AdmiralLuckytiger/OsciBoard/Documentation/Images/Full Wave Precision Rectifier/A.jpeg

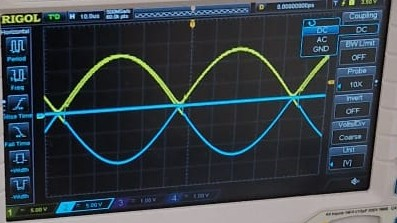
Documentation/Images/Full Wave Precision Rectifier/A.jpeg
