AdmiralLuckytiger/OsciBoard/Documentation/Images/Full Wave Precision Rectifier/B.jpeg

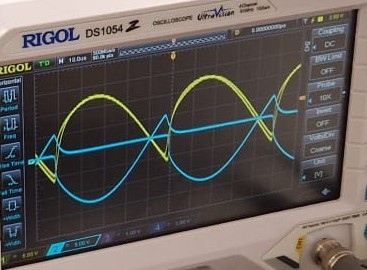
Documentation/Images/Full Wave Precision Rectifier/B.jpeg
