AdmiralLuckytiger/OsciBoard/Documentation/Images/PCB/PCB_B_v1.png

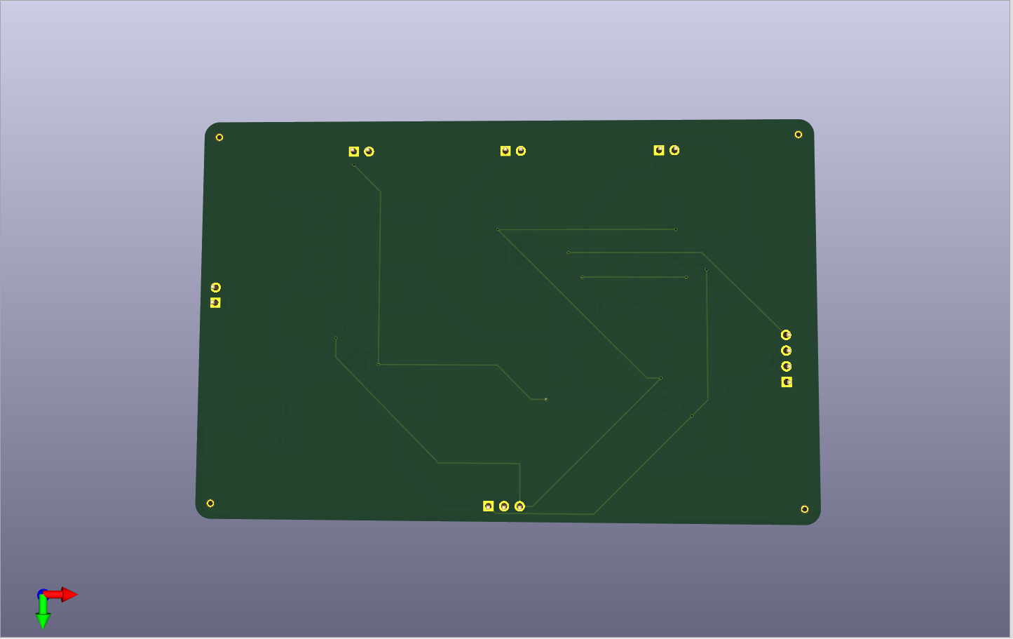
Documentation/Images/PCB/PCB_B_v1.png
