AdmiralLuckytiger/OsciBoard/Documentation/Images/PCB/PCB_B_v2.png

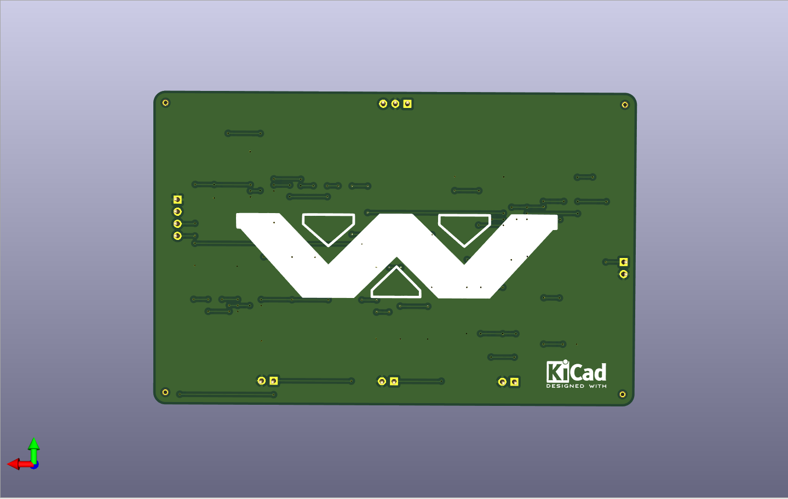
Documentation/Images/PCB/PCB_B_v2.png
