AdmiralLuckytiger/OsciBoard/Documentation/Images/PCB/PCB_B_v3.png

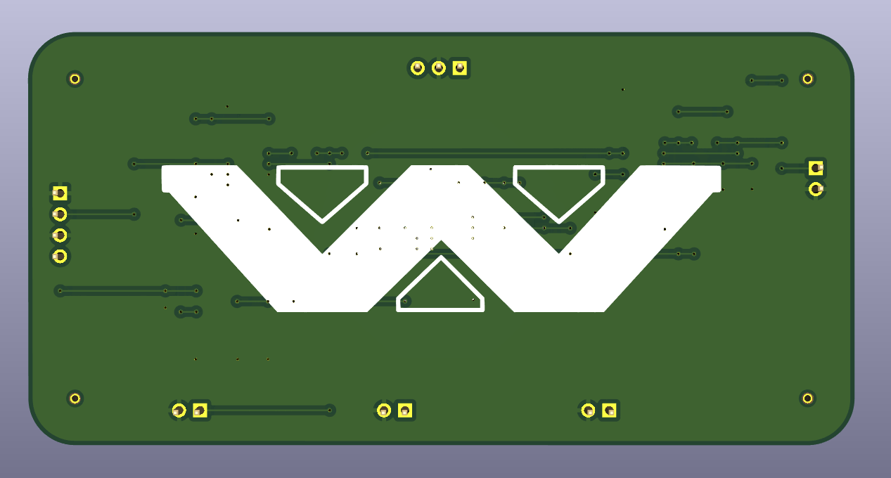
Documentation/Images/PCB/PCB_B_v3.png
