AdmiralLuckytiger/OsciBoard/Documentation/Images/PCB/PCB_F_v1.png

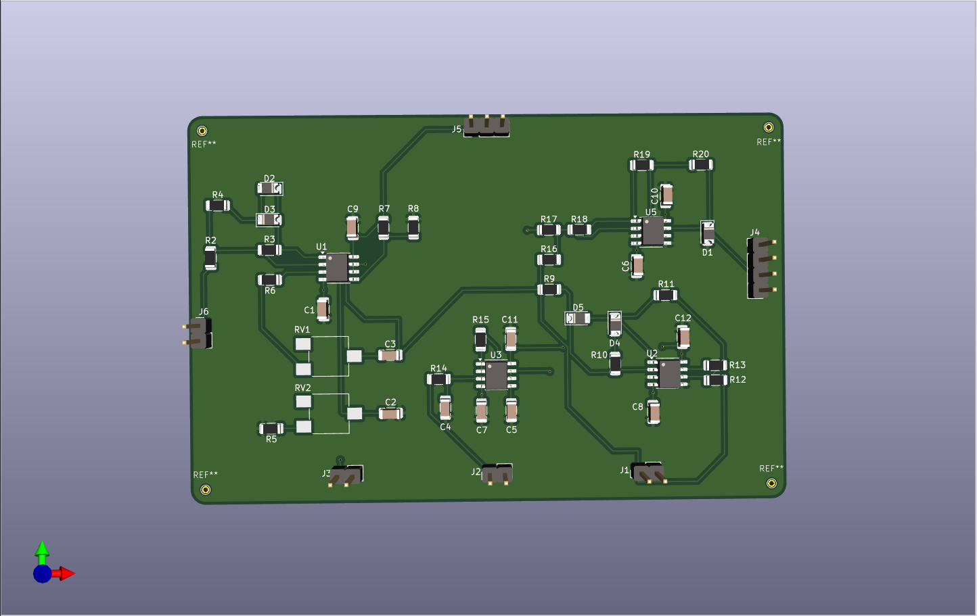
Documentation/Images/PCB/PCB_F_v1.png
