AdmiralLuckytiger/OsciBoard/Documentation/Images/PCB/PCB_F_v2.png

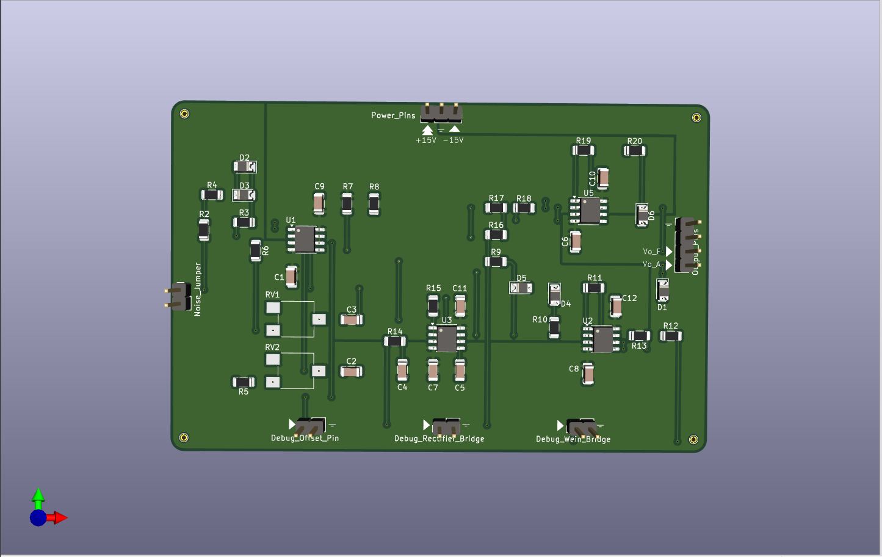
Documentation/Images/PCB/PCB_F_v2.png
