AdmiralLuckytiger/OsciBoard/Documentation/Images/PCB/PCB_F_v3.png

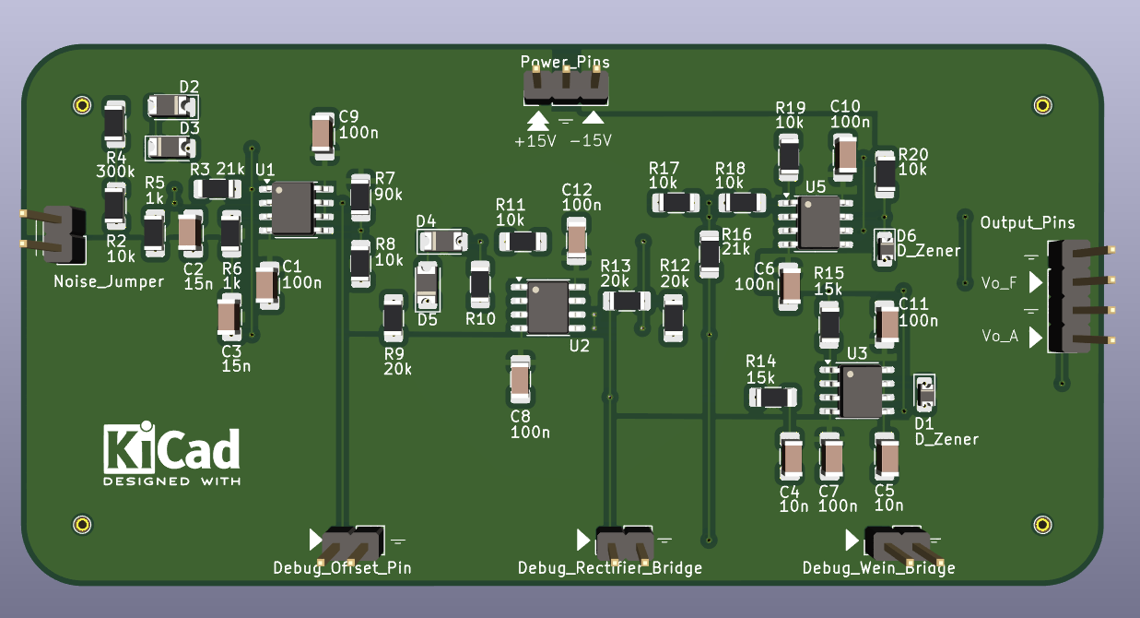
Documentation/Images/PCB/PCB_F_v3.png
