AdmiralLuckytiger/OsciBoard/Documentation/Images/Wein Bridge Oscillator/A.jpg

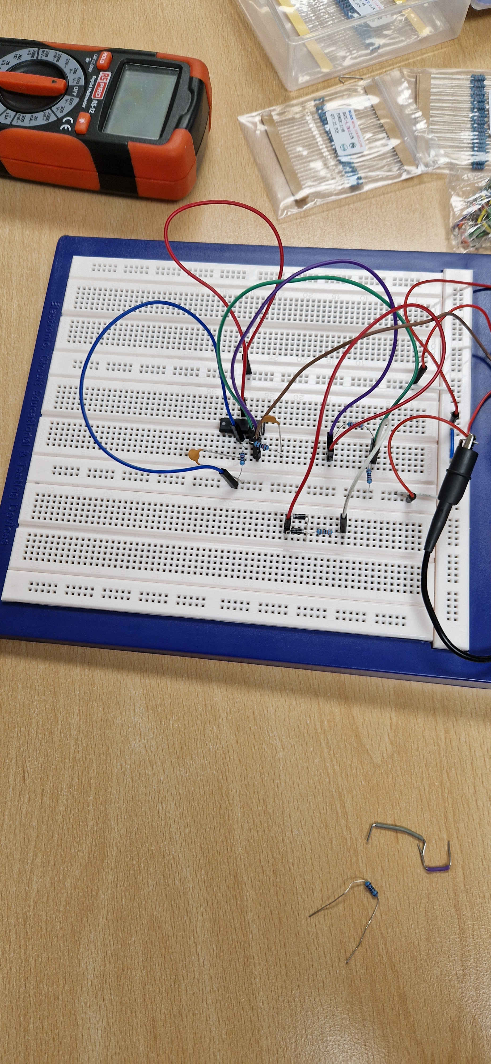
Documentation/Images/Wein Bridge Oscillator/A.jpg
