AdmiralLuckytiger/OsciBoard/Documentation/Images/Wein Bridge Oscillator/B.jpg

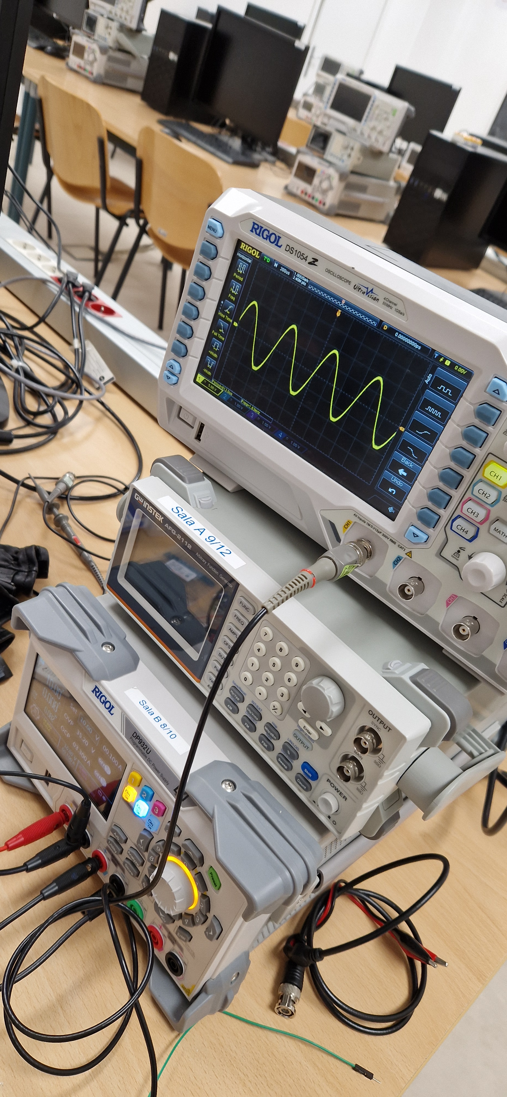
Documentation/Images/Wein Bridge Oscillator/B.jpg
