AdmiralLuckytiger/OsciBoard/Documentation/Images/Wein Bridge Oscillator/C.jpg

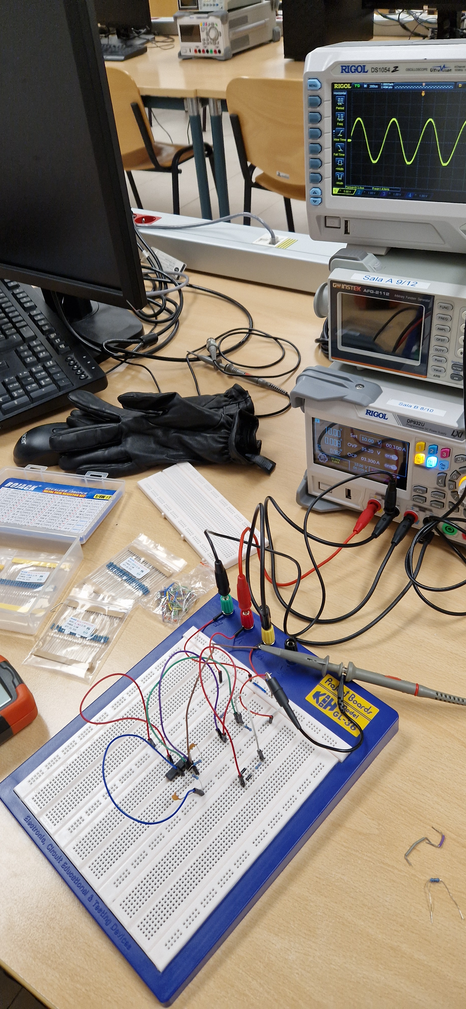
Documentation/Images/Wein Bridge Oscillator/C.jpg
