AdmiralLuckytiger/OsciBoard/Documentation/Images/Wein Bridge Oscillator/D.jpg

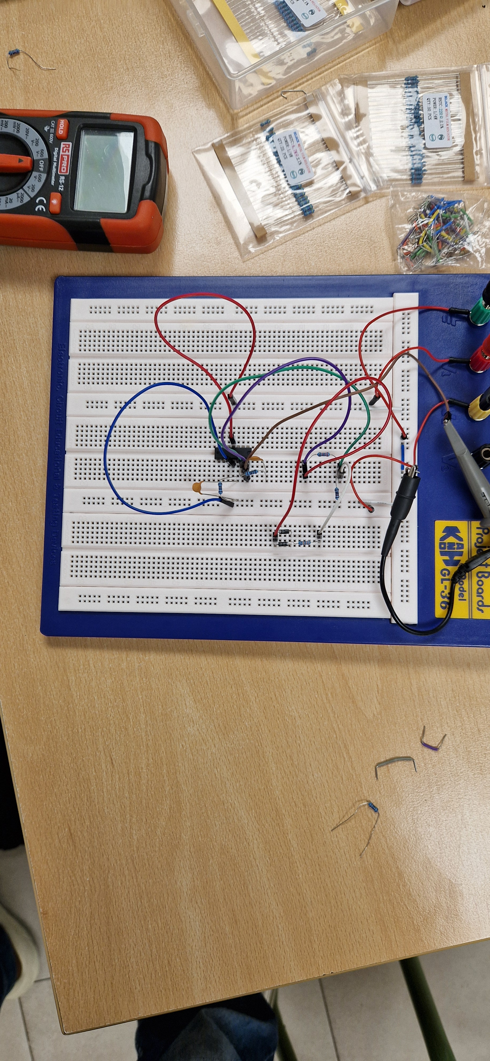
Documentation/Images/Wein Bridge Oscillator/D.jpg
