AdmiralLuckytiger/OsciBoard/Documentation/Images/Wein Bridge Oscillator/E.jpg

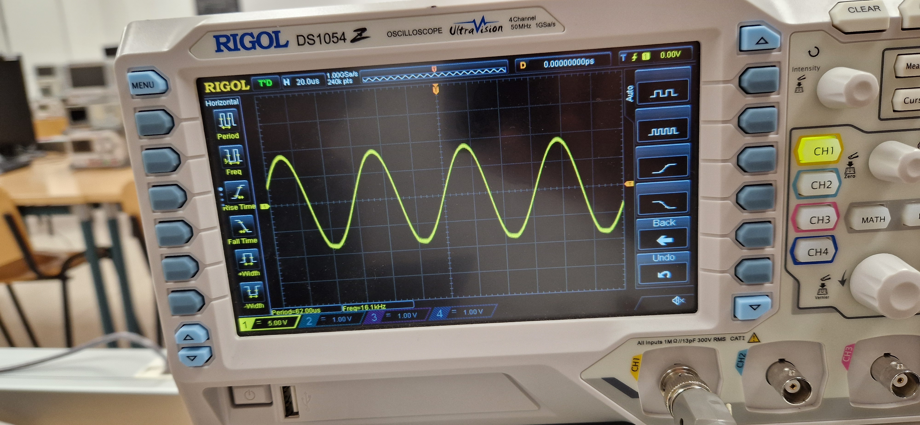
Documentation/Images/Wein Bridge Oscillator/E.jpg
