AdmiralLuckytiger/OsciBoard/Documentation/Images/Wein Bridge Oscillator/F.jpg

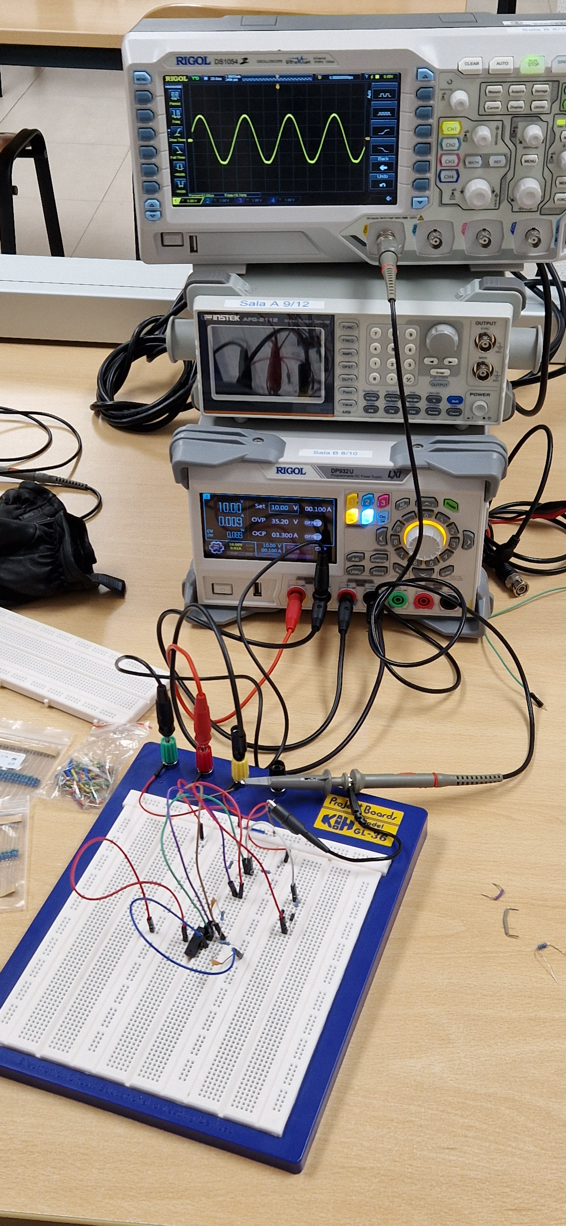
Documentation/Images/Wein Bridge Oscillator/F.jpg
