AdmiralLuckytiger/OsciBoard/Documentation/Images/Wein Bridge Oscillator/G.jpeg

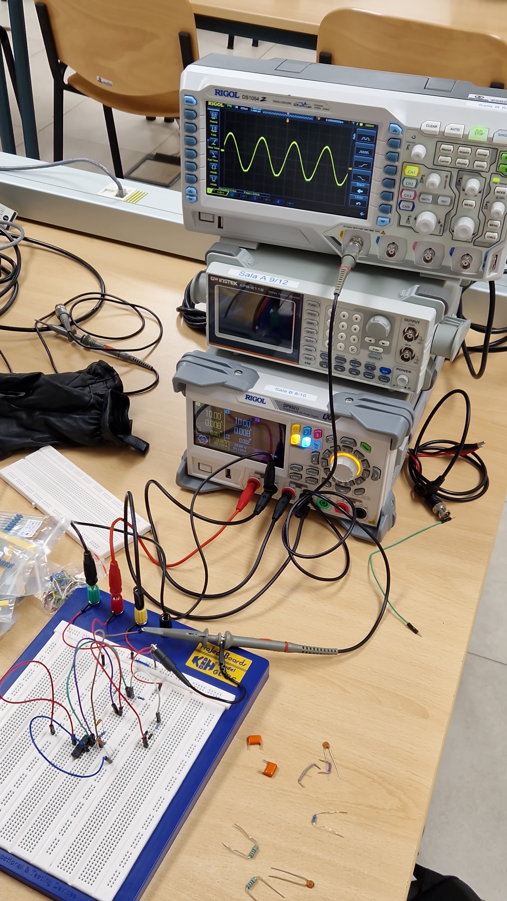
Documentation/Images/Wein Bridge Oscillator/G.jpeg
