AdmiralLuckytiger/OsciBoard/Documentation/Images/Wein Bridge Oscillator/H.jpeg

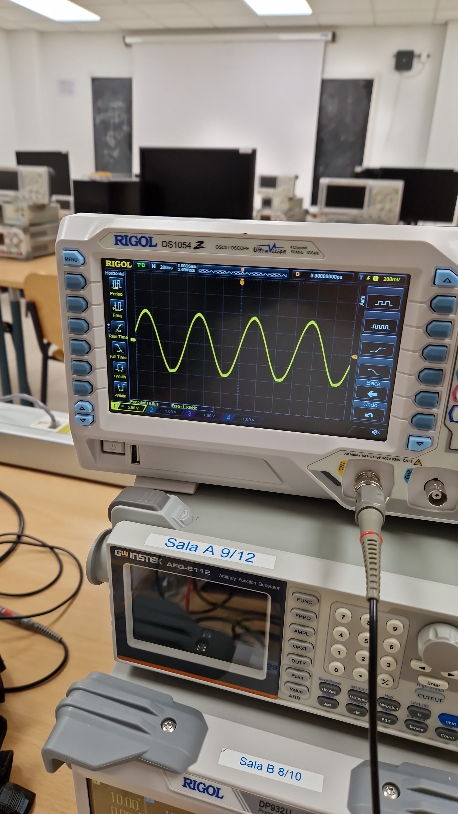
Documentation/Images/Wein Bridge Oscillator/H.jpeg
