AdmiralLuckytiger/OsciBoard/Documentation/Images/XADC_tutorial/50KSPS-5SPP.png

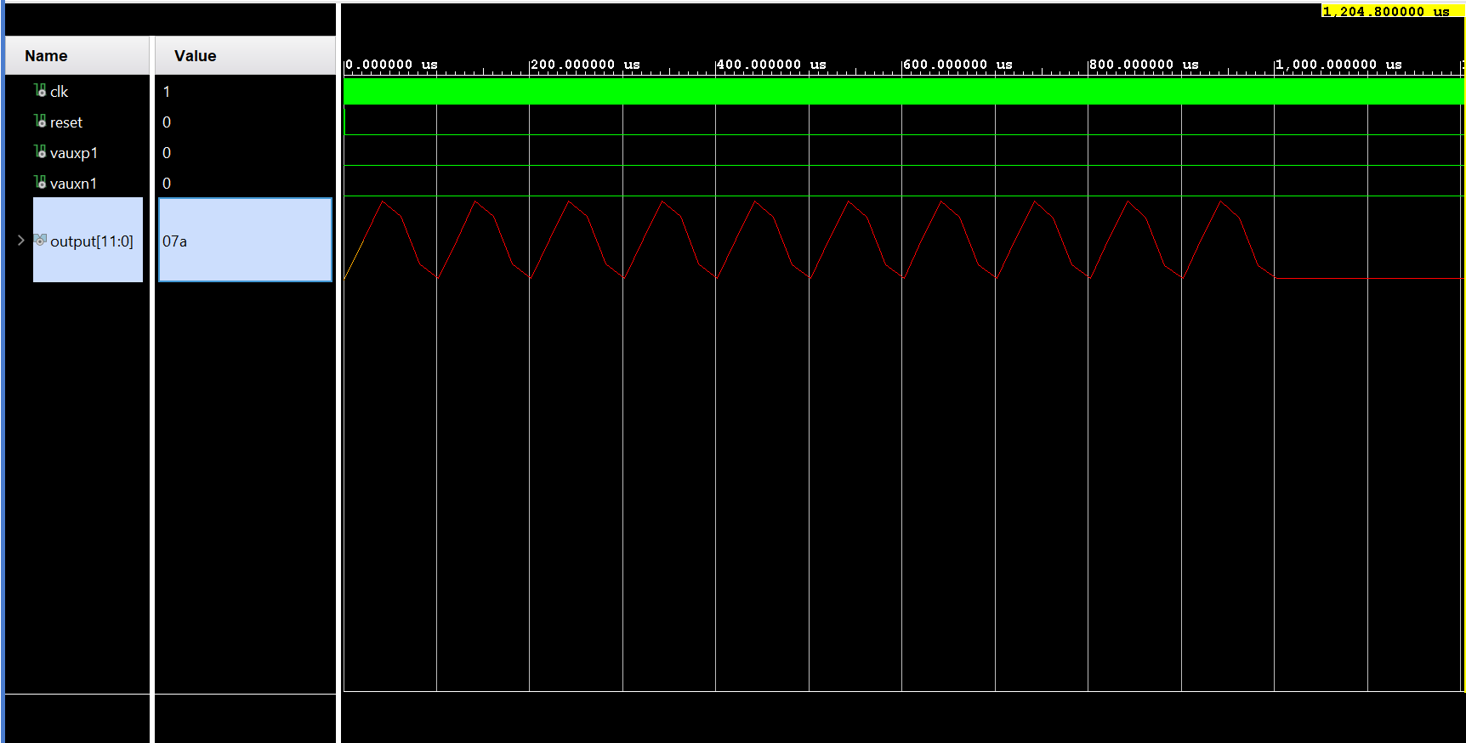
Documentation/Images/XADC_tutorial/50KSPS-5SPP.png
