AdmiralLuckytiger/OsciBoard/Documentation/Images/XADC_tutorial/500KSPS-50SPP.png

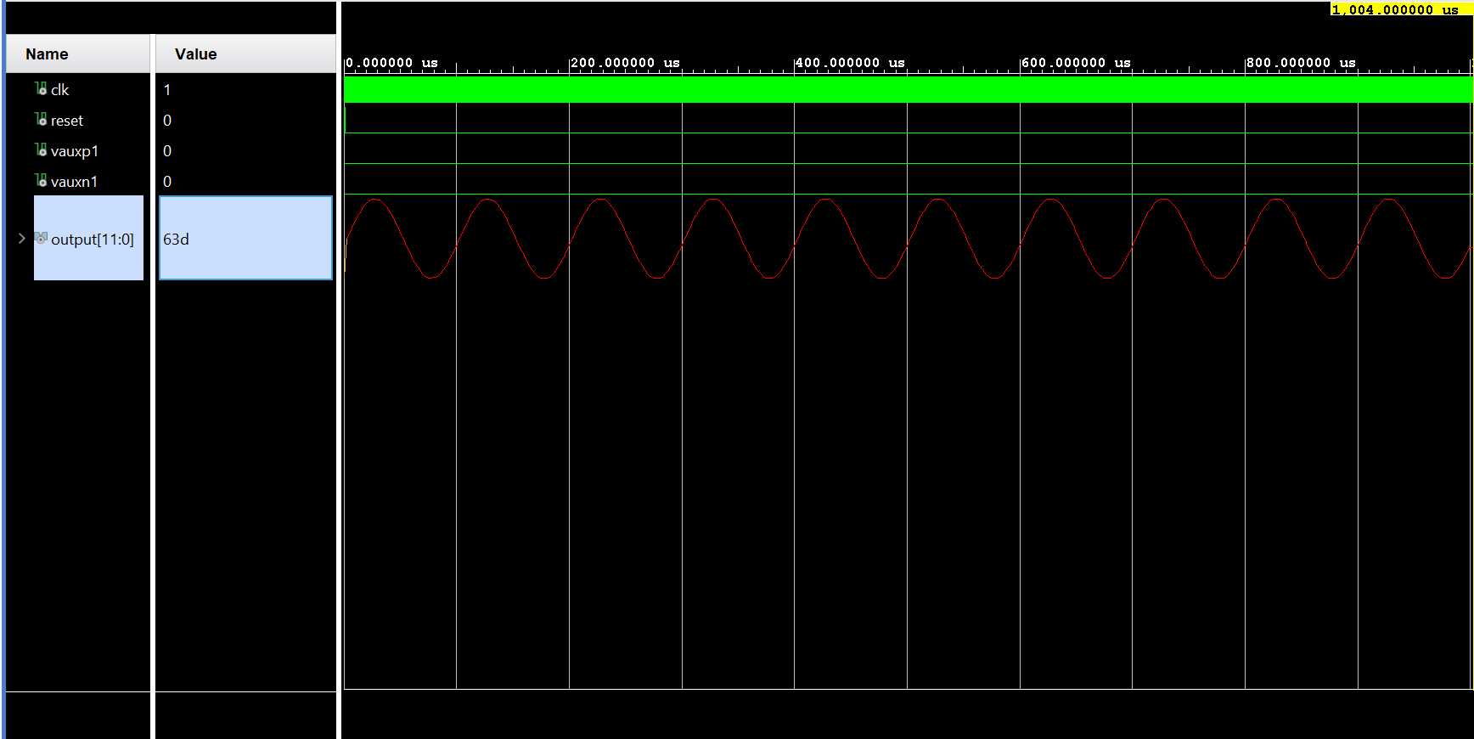
Documentation/Images/XADC_tutorial/500KSPS-50SPP.png
