AdmiralLuckytiger/OsciBoard/Documentation/Images/XADC_tutorial/Decimal signal.png

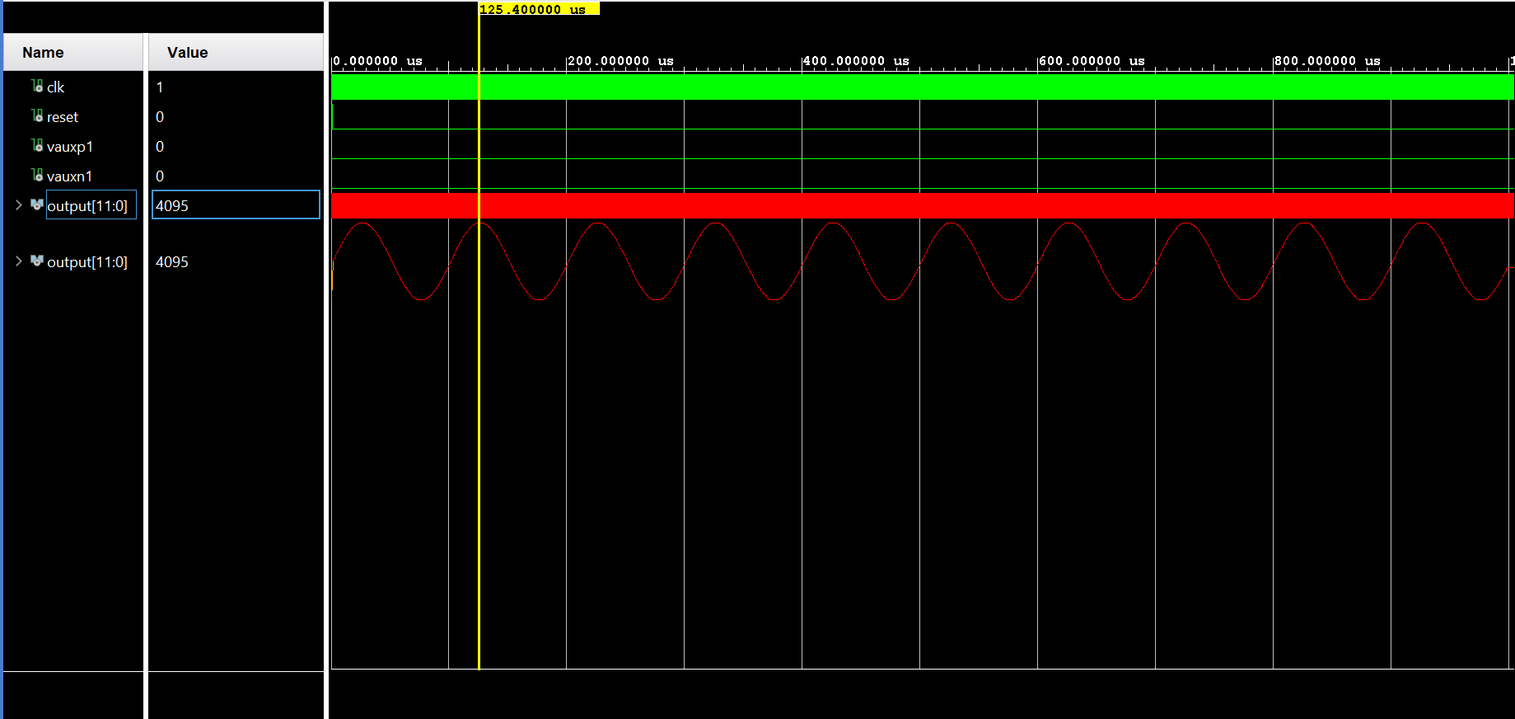
Documentation/Images/XADC_tutorial/Decimal signal.png
