AdmiralLuckytiger/OsciBoard/Documentation/Images/XADC_tutorial/Step_1A.png

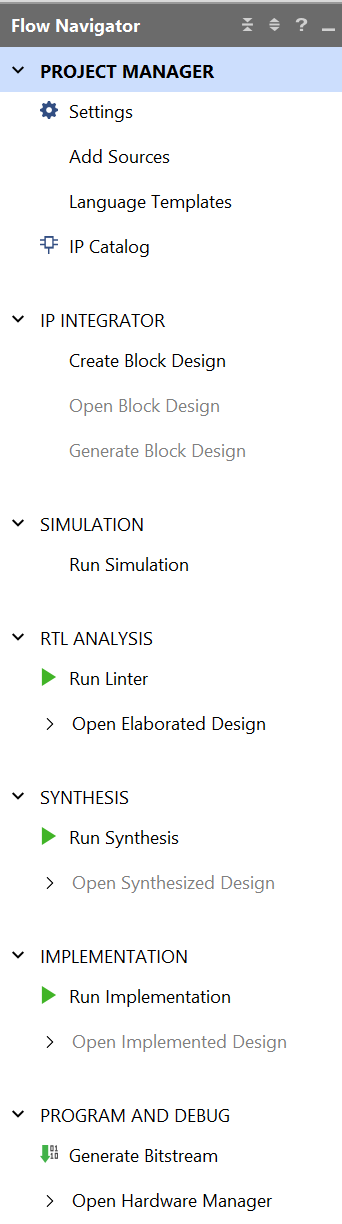
Documentation/Images/XADC_tutorial/Step_1A.png
