AdmiralLuckytiger/OsciBoard/Documentation/Images/XADC_tutorial/Step_2C.png

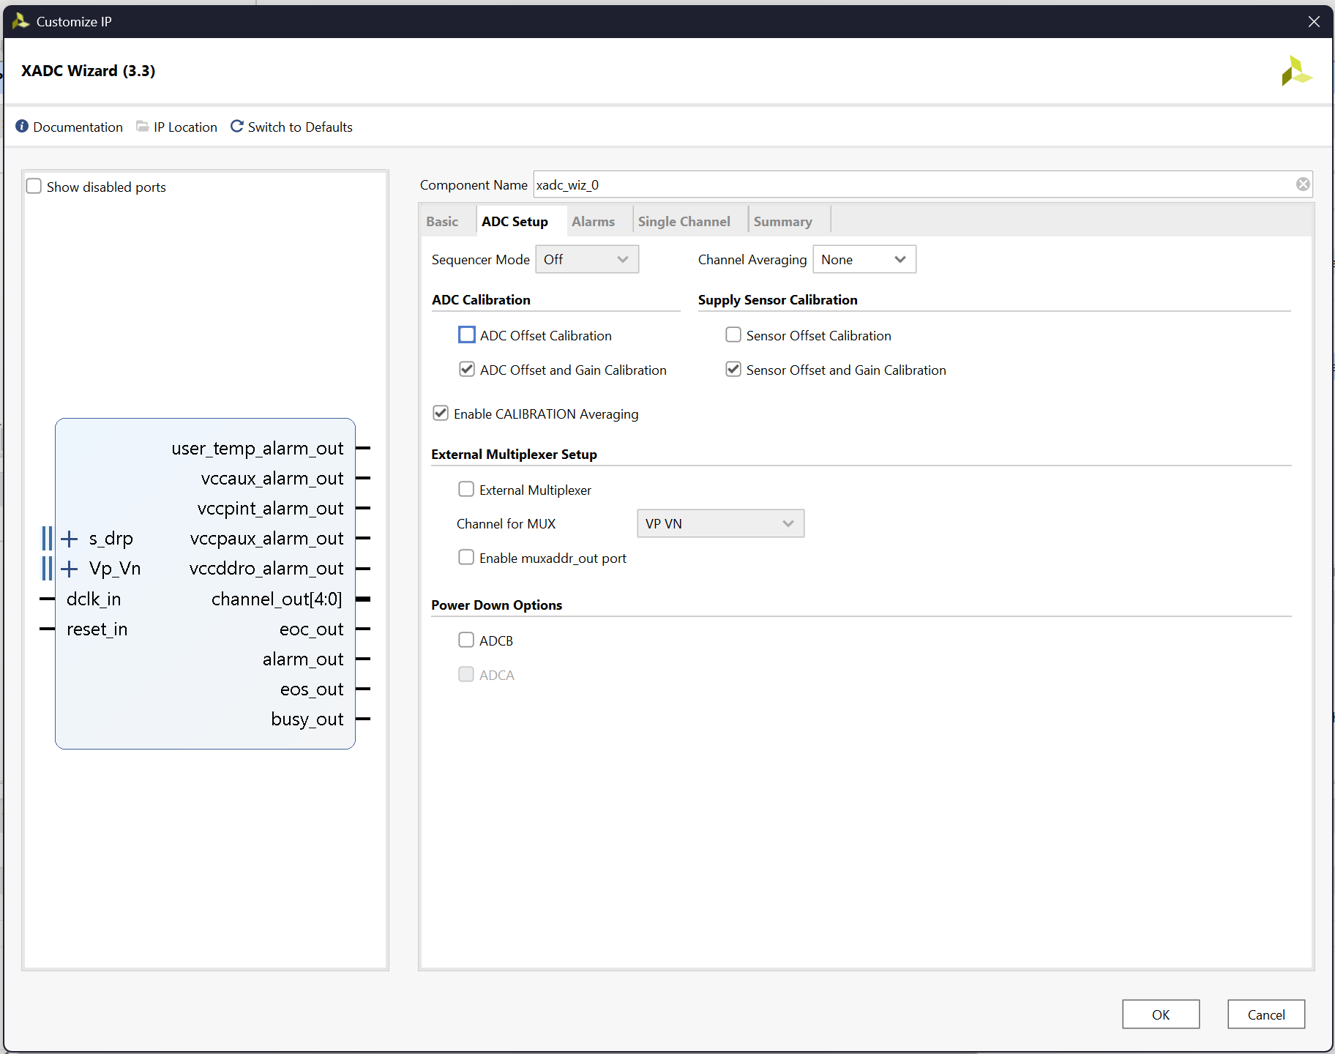
Documentation/Images/XADC_tutorial/Step_2C.png
