AdmiralLuckytiger/OsciBoard/Documentation/Images/XADC_tutorial/Step_2E.png

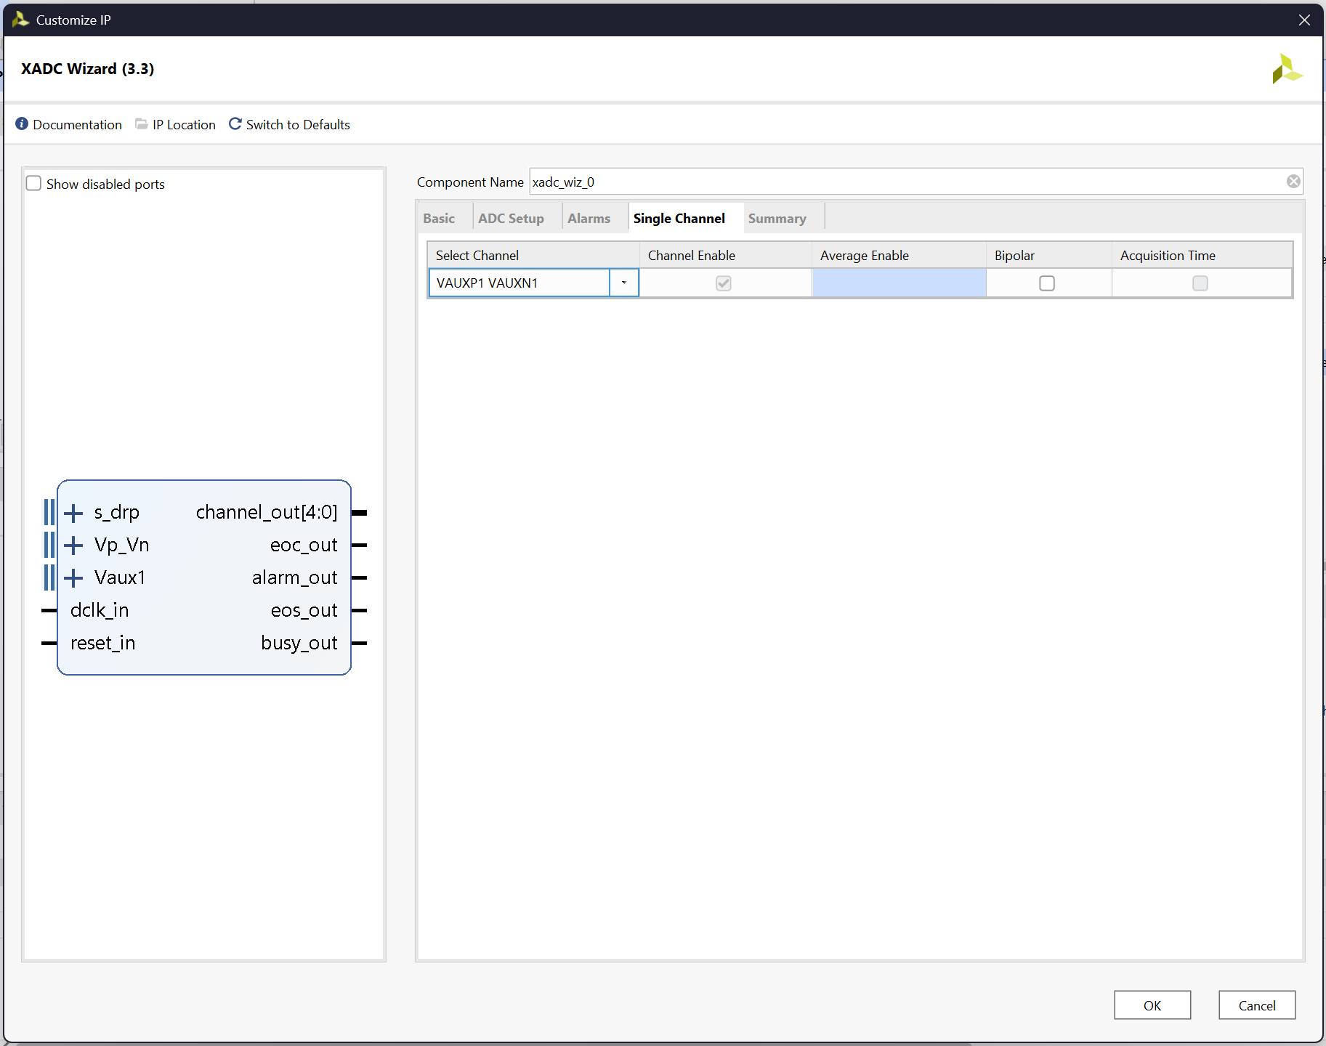
Documentation/Images/XADC_tutorial/Step_2E.png
