AdmiralLuckytiger/OsciBoard/Documentation/Images/XADC_tutorial/Step_2F.png

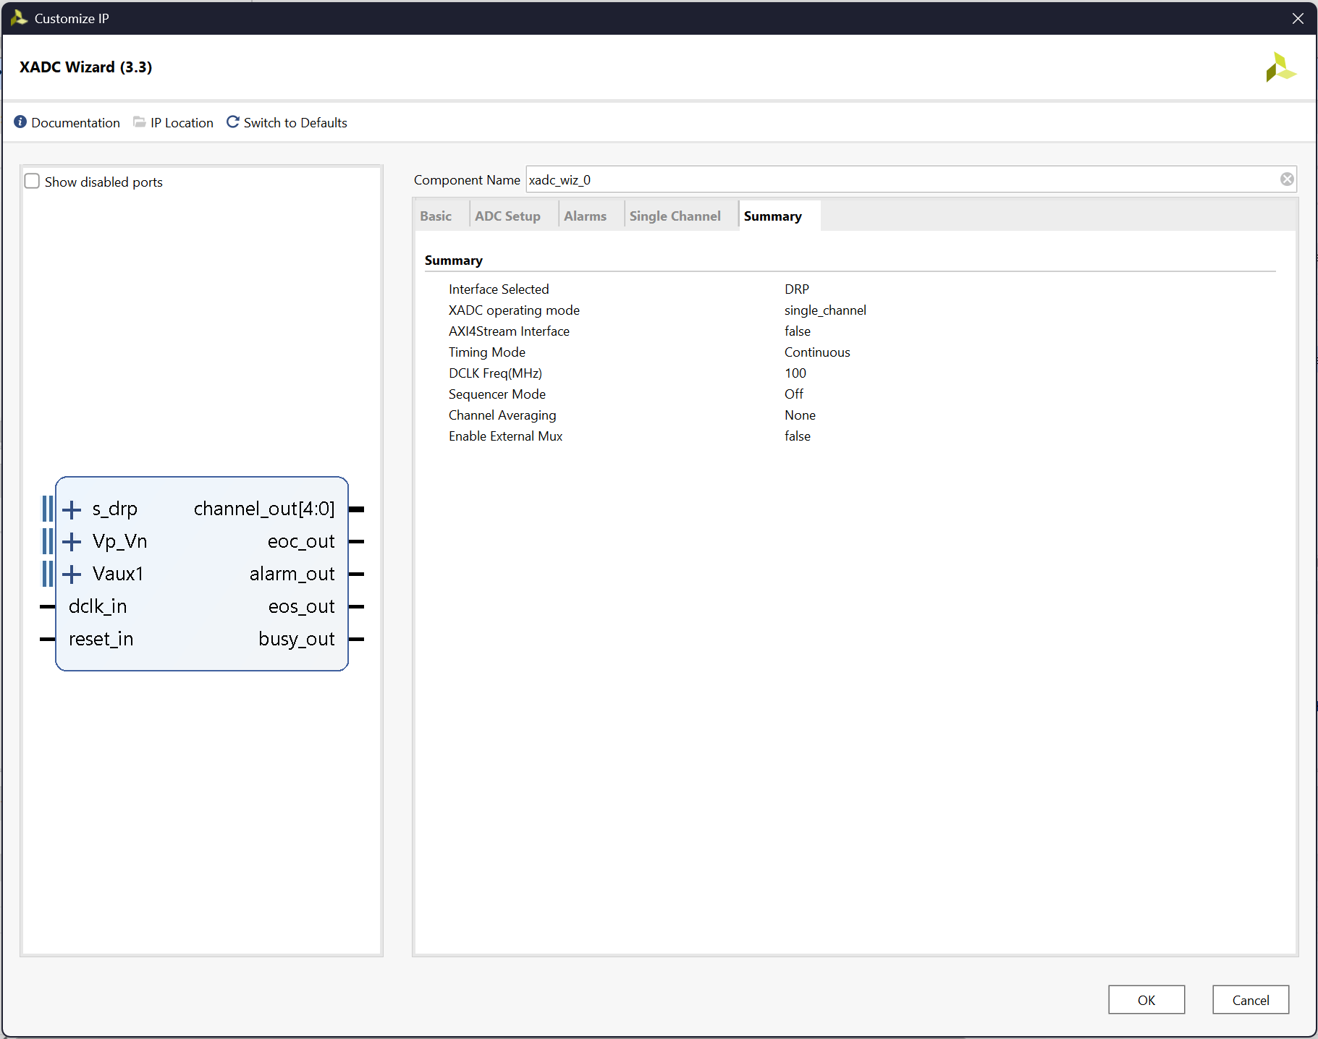
Documentation/Images/XADC_tutorial/Step_2F.png
