AdmiralLuckytiger/OsciBoard/Documentation/Images/XADC_tutorial/Step_3.png

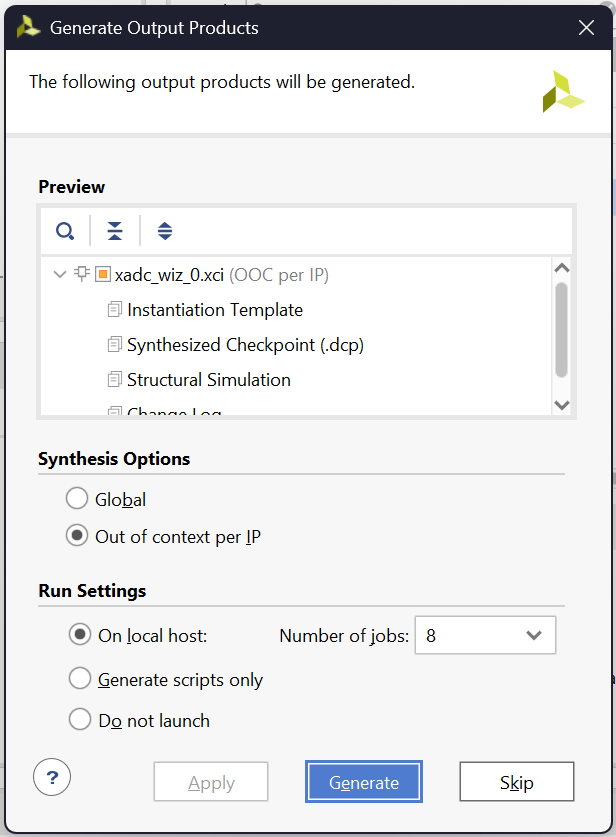
Documentation/Images/XADC_tutorial/Step_3.png
