AdmiralLuckytiger/OsciBoard/Documentation/Images/XADC_tutorial/Step_4C.png

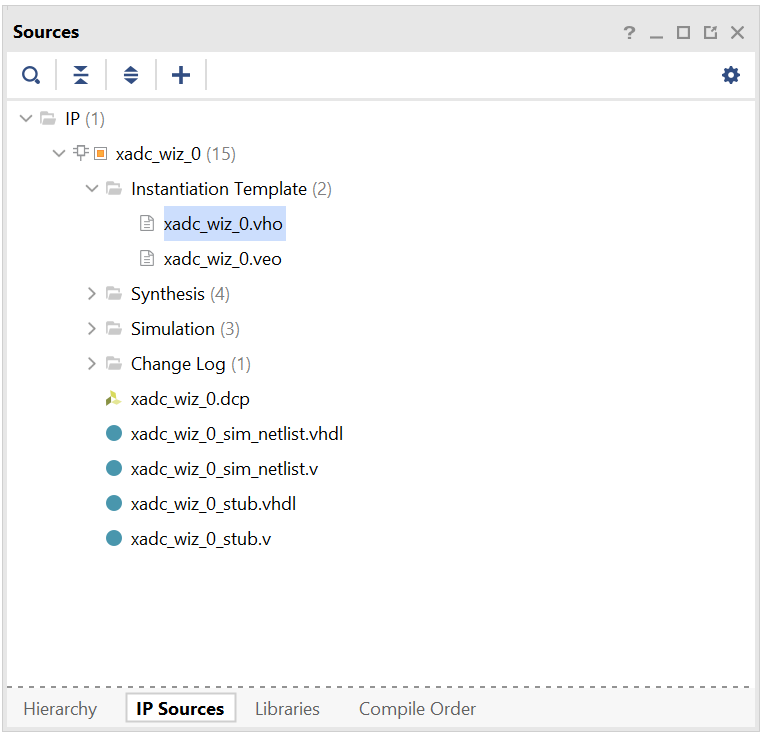
Documentation/Images/XADC_tutorial/Step_4C.png
