AdmiralLuckytiger/OsciBoard/Documentation/Images/XADC_tutorial/Step_5.png

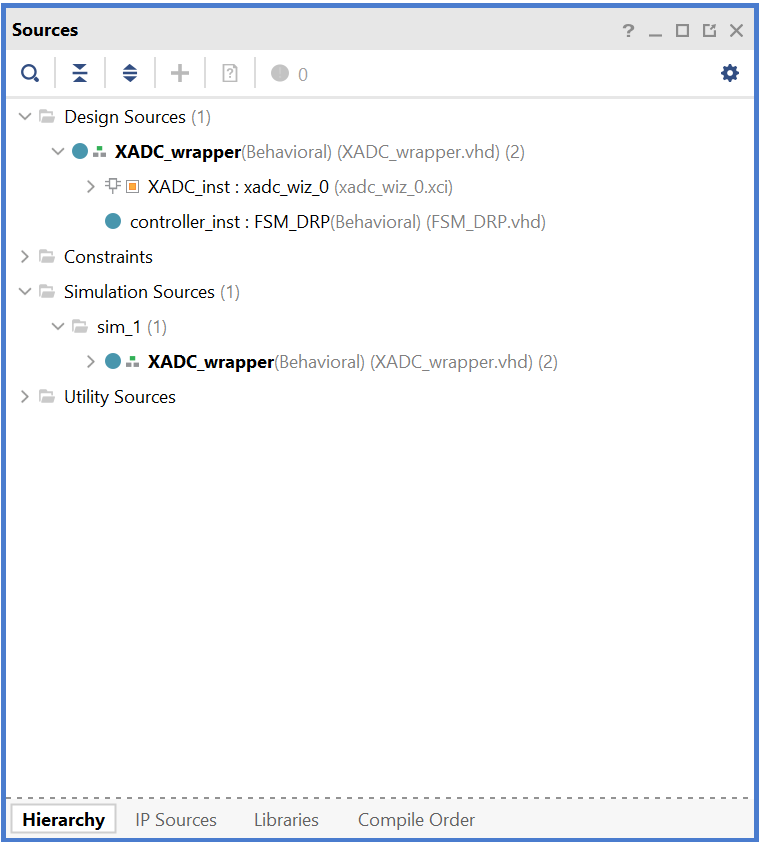
Documentation/Images/XADC_tutorial/Step_5.png
