AdmiralLuckytiger/OsciBoard/Documentation/Images/XADC_tutorial/Step_6.png

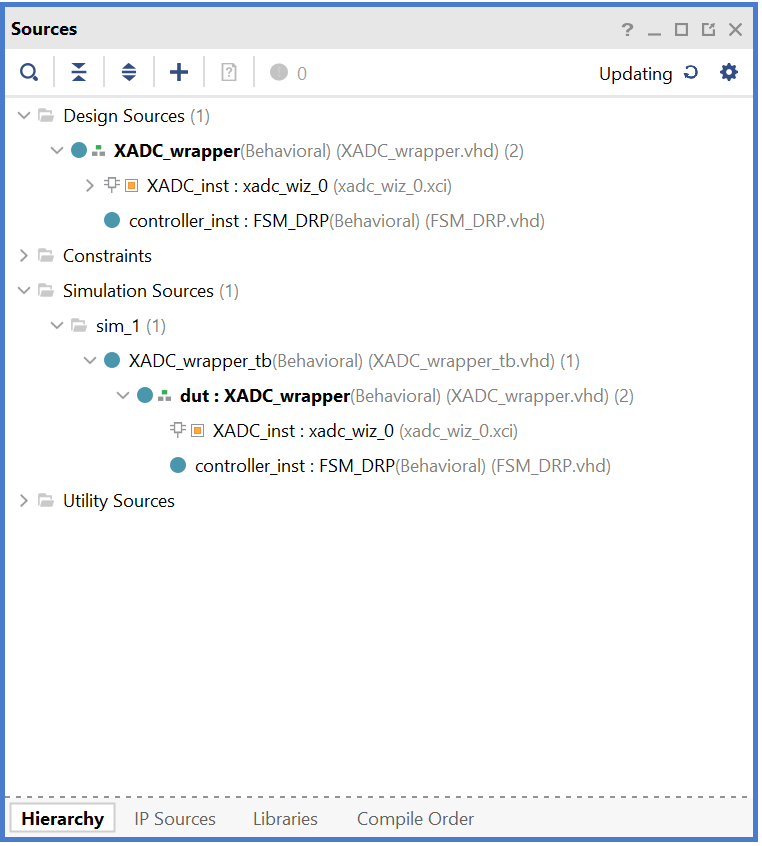
Documentation/Images/XADC_tutorial/Step_6.png
