AdmiralLuckytiger/OsciBoard/Documentation/Images/XADC_tutorial/Step_7A.png

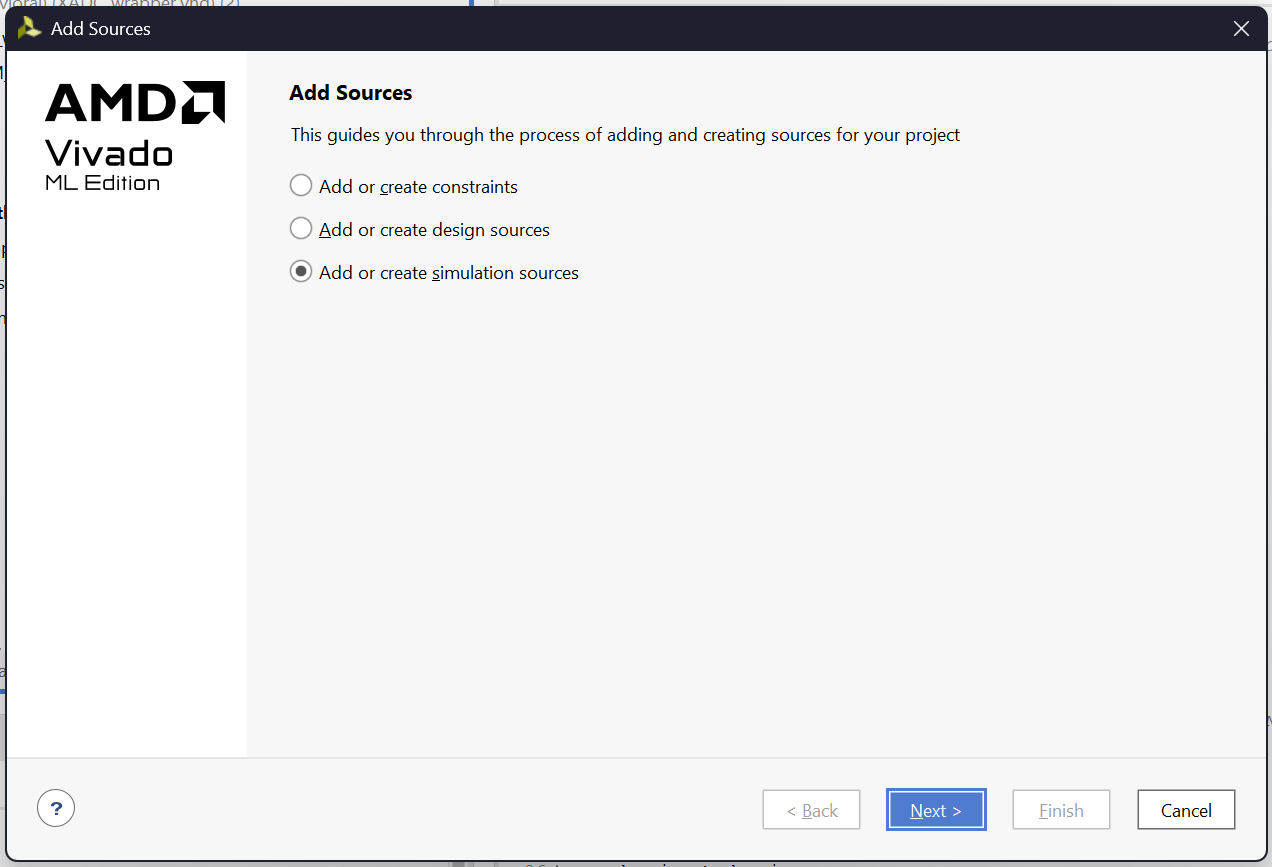
Documentation/Images/XADC_tutorial/Step_7A.png
