AdmiralLuckytiger/OsciBoard/Documentation/Images/XADC_tutorial/Step_7B.png

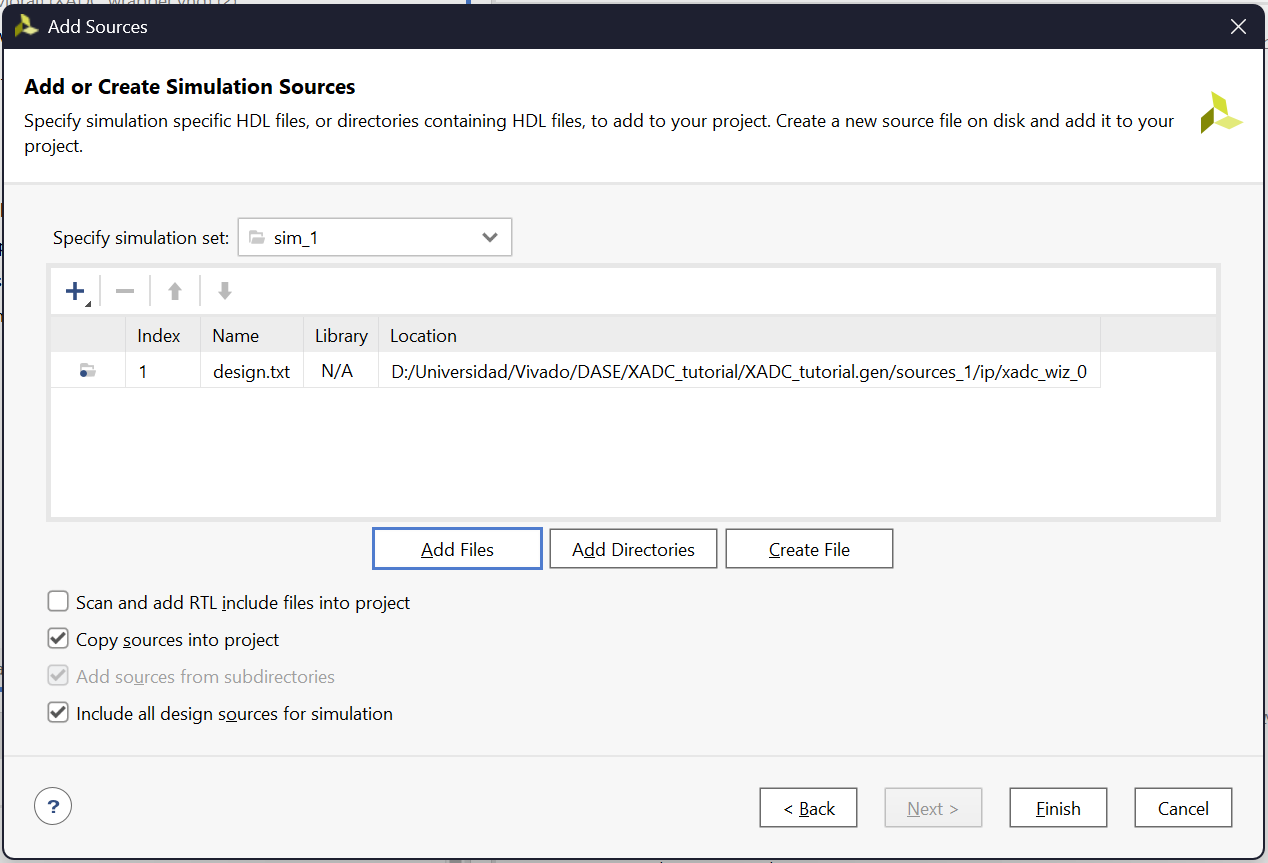
Documentation/Images/XADC_tutorial/Step_7B.png
