AdmiralLuckytiger/OsciBoard/Documentation/Images/XADC_tutorial/Step_7C.png

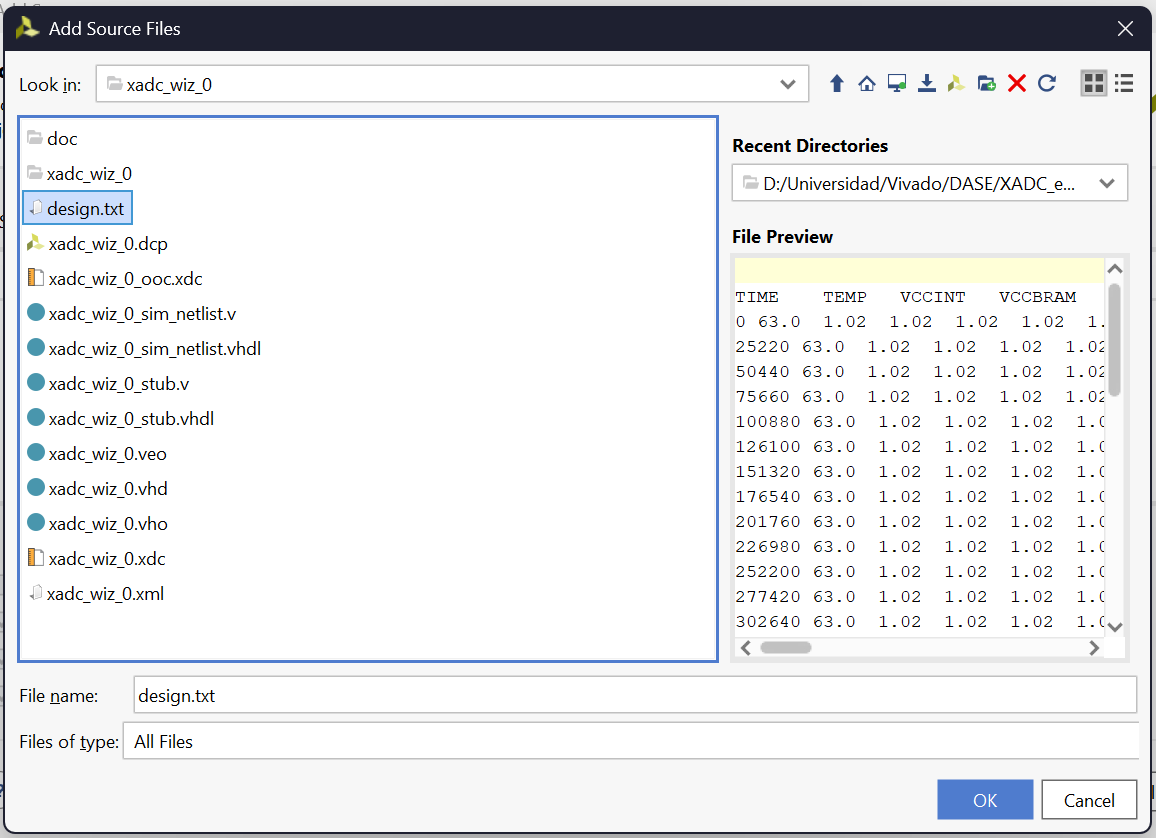
Documentation/Images/XADC_tutorial/Step_7C.png
