AdmiralLuckytiger/OsciBoard/Documentation/Images/XADC_tutorial/Step_7D.png

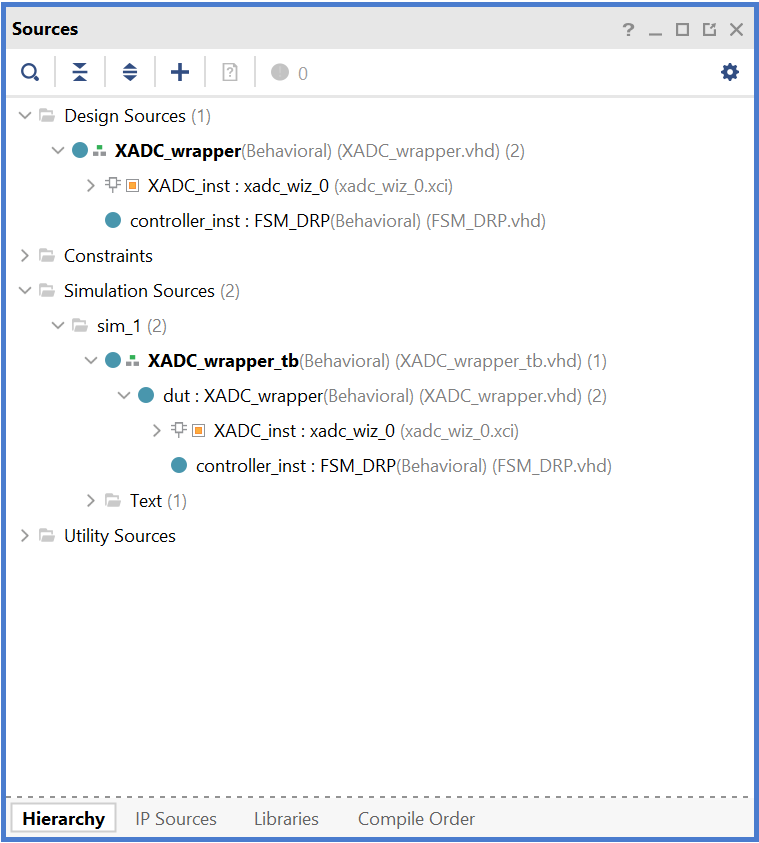
Documentation/Images/XADC_tutorial/Step_7D.png
