AdmiralLuckytiger/OsciBoard/Documentation/Images/XADC_tutorial/Step_8.png

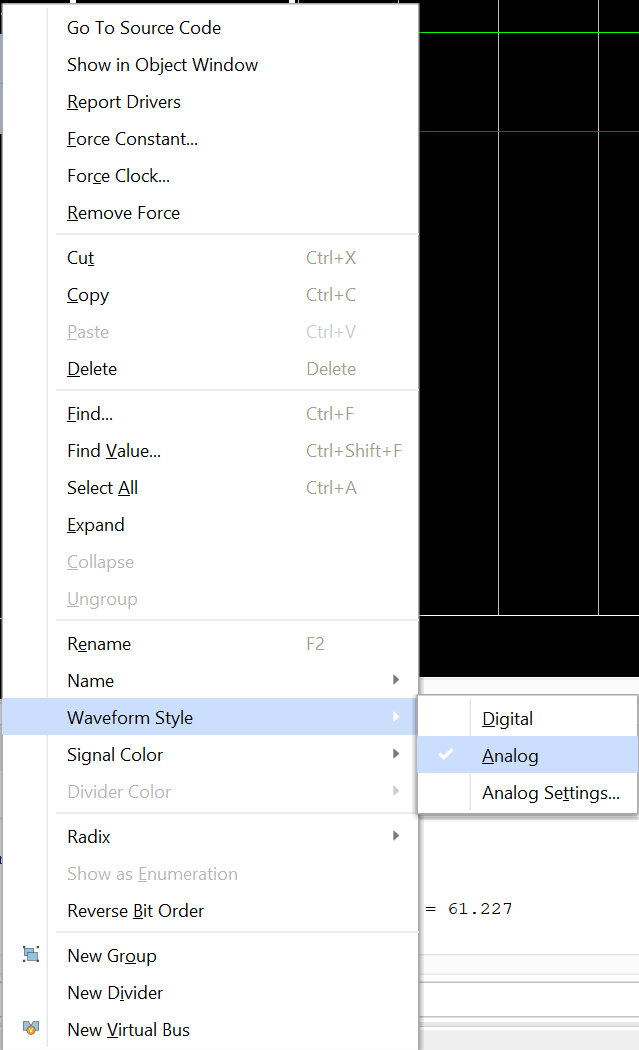
Documentation/Images/XADC_tutorial/Step_8.png
